Av1zi/Ebeep/include/Callbacks.h

#pragma once
#include <esp_sleep.h>
#include <time.h>

// ═══════════════════════════════════════════════════════════════
//  Callbacks.h
//  Buttons, display refresh, MQTT callbacks, and deep-sleep power
//  management — merged into one file so every function is defined
//  before it's used (checkButtons() and drawCurrentScreen() are
//  needed by the power-management refresh helpers below them).
//  Must be included AFTER all state files.
// ═══════════════════════════════════════════════════════════════

static float battVoltageEma = 0;  // mV, actual pack voltage (post-divider math)

void updateBattery() {
  // 8 samples is enough noise averaging on its own — the EMA below does
  // the real smoothing across calls, so we don't burn extra ADC time here.
  uint32_t sum = 0;
  for (int i = 0; i < 8; i++) sum += analogReadMilliVolts(A0);
  const float vBatSample = (sum / 8.0f) * BATTERY_DIVIDER_RATIO;

  battVoltageEma = (battVoltageEma == 0)
                     ? vBatSample
                     : battVoltageEma + BATTERY_EMA_ALPHA * (vBatSample - battVoltageEma);

  batteryPct = (int)((battVoltageEma - BATTERY_MIN_MV) * 100.0f / (BATTERY_MAX_MV - BATTERY_MIN_MV));
  batteryPct = constrain(batteryPct, 0, 100);
}

// Resets the active-mode timer. Call on any button press or incoming message.
void markActivity() {
  lastActivityMillis = millis();
}


bool pendingLeft  = false;
bool pendingMid   = false;
bool pendingRight = false;
bool isRefreshing = false;

// ── Button Handler ────────────────────────────────────────────
// Defined first so refreshDisplay() can call it.
void checkButtons() {
  bool curLeft  = digitalRead(BTN_LEFT);
  bool curMid   = digitalRead(BTN_SELECT);
  bool curRight = digitalRead(BTN_RIGHT);

  bool leftPressed  = (curLeft  == LOW && lastLeft  == HIGH);
  bool midPressed   = (curMid   == LOW && lastMid   == HIGH);
  bool rightPressed = (curRight == LOW && lastRight == HIGH);

  const unsigned long now = millis();

  if ((leftPressed || midPressed || rightPressed) && (now - lastBtnTime > DEBOUNCE_MS)) {
    lastBtnTime = now;
    markActivity();  // any press keeps the device in the active (modem-sleep) tier
    if (isRefreshing) {
      pendingLeft  |= leftPressed;
      pendingMid   |= midPressed;
      pendingRight |= rightPressed;
    } else {
      if (leftPressed || rightPressed) {
        heldButton    = leftPressed ? -1 : 1;
        holdStartTime = now;
        lastRepeatAt  = now;
      } else {
        heldButton = 0;
      }

      switch (currentState) {
        case STATE_HOME:      handleHomeInput      (leftPressed, midPressed, rightPressed); break;
        case STATE_INBOX:     handleInboxInput     (leftPressed, midPressed, rightPressed); break;
        case STATE_COMPOSE:   handleComposeInput   (leftPressed, midPressed, rightPressed); break;
        case STATE_SENT:      handleSentInput      (leftPressed, midPressed, rightPressed); break;
        case STATE_GAMES:     handleGamesInput     (leftPressed, midPressed, rightPressed); break;
        case STATE_TICTACTOE: handleTicTacToeInput (leftPressed, midPressed, rightPressed); break;
        case STATE_CONNECT4:  handleConnect4Input  (leftPressed, midPressed, rightPressed); break;
        case STATE_BLACKJACK: handleBlackjackInput(leftPressed, midPressed, rightPressed); break;
        default: break;
      }
    }
  }

  // Hold-scroll repeat (Compose, Games, and in-game selectors)
  if (heldButton != 0 &&
      (currentState == STATE_COMPOSE || currentState == STATE_GAMES ||
       currentState == STATE_TICTACTOE || currentState == STATE_CONNECT4 ||
       currentState == STATE_BLACKJACK)) {
    const bool stillHeld = (heldButton == -1) ? (curLeft == LOW) : (curRight == LOW);

    if (!stillHeld) {
      heldButton = 0;
    } else if ((now - holdStartTime >= HOLD_DELAY_MS) &&
               (now - lastRepeatAt  >= HOLD_REPEAT_MS)) {
      lastRepeatAt = now;
      const bool fL = (heldButton == -1);
      const bool fR = (heldButton ==  1);
      switch (currentState) {
        case STATE_COMPOSE:   handleComposeInput   (fL, false, fR); break;
        case STATE_GAMES:     handleGamesInput     (fL, false, fR); break;
        case STATE_TICTACTOE: handleTicTacToeInput (fL, false, fR); break;
        case STATE_CONNECT4:  handleConnect4Input  (fL, false, fR); break;
        case STATE_BLACKJACK: handleBlackjackInput (fL, false, fR); break;
        default: break;
      }
    }
  }

  lastLeft  = curLeft;
  lastMid   = curMid;
  lastRight = curRight;
}


// Draws whatever the current screen state is.
void drawCurrentScreen() {
  switch (currentState) {
    case STATE_HOME:      drawHome();      break;
    case STATE_INBOX:     drawInbox();     break;
    case STATE_COMPOSE:   drawCompose();   break;
    case STATE_SENT:      drawSent();      break;
    case STATE_GAMES:     drawGames();     break;
    case STATE_WIFI:      drawWifi();      break;
    case STATE_TICTACTOE: drawTicTacToe(); break;
    case STATE_CONNECT4:  drawConnect4();  break;
    case STATE_BLACKJACK: drawBlackjack(); break;
  }
}


// ── Display Refresh ───────────────────────────────────────────
// Calls checkButtons() mid-refresh so button presses aren't lost
// while the e-ink panel is transferring data.
void refreshDisplay() {
  isRefreshing = true;

  if (fastUpdate) {
    display.setPartialWindow(0, CONTENT_Y + 2, SCREEN_W, SCREEN_H - CONTENT_Y);
  } else {
    display.setFullWindow();
  }

  display.firstPage();
  do {
    display.fillScreen(GxEPD_WHITE);
    if (!fastUpdate) drawStatusBar(batteryPct);
    drawCurrentScreen();
    checkButtons();
  } while (display.nextPage());

  fastUpdate = false;
  isRefreshing = false;

  // Replay any button pressed during refresh
   if (pendingLeft || pendingMid || pendingRight) {
    bool l = pendingLeft, m = pendingMid, r = pendingRight;
    pendingLeft = pendingMid = pendingRight = false;
    switch (currentState) {
      case STATE_HOME:      handleHomeInput(l, m, r);       break;
      case STATE_INBOX:     handleInboxInput(l, m, r);      break;
      case STATE_COMPOSE:   handleComposeInput(l, m, r);    break;
      case STATE_SENT:      handleSentInput(l, m, r);       break;
      case STATE_GAMES:     handleGamesInput(l, m, r);      break;
      case STATE_TICTACTOE: handleTicTacToeInput(l, m, r);  break;
      case STATE_CONNECT4:  handleConnect4Input  (l, m, r); break;
      case STATE_BLACKJACK: handleBlackjackInput(l, m, r); break;
      default: break;
    }
  }
}


// ═══════════════════════════════════════════════════════════════
//  Power Management
//
//  Tiers, checked in priority order:
//    1. Active   — no deep sleep, WiFi modem-sleep only, for
//                  ACTIVE_TIMEOUT_MS after a button press or message.
//    2. Low batt — wake every WAKE_INTERVAL_LOWBATT_S  (batt < LOW_BATT_PCT)
//    3. Night    — wake every WAKE_INTERVAL_NIGHT_S    (00:00-08:00)
//    4. Default  — wake every WAKE_INTERVAL_DEFAULT_S
// ═══════════════════════════════════════════════════════════════

RTC_DATA_ATTR bool clockSynced = false;  // NTP only needs to succeed once — RTC keeps ticking through deep sleep
RTC_DATA_ATTR bool wifiWasOk   = true;   // persists across deep sleep — lets quickCheckAndMaybeSleep() tell if connectivity flipped since the last wake

bool isNightHours() {
  time_t now = time(nullptr);
  if (now < 100000) return false;
  struct tm t;
  localtime_r(&now, &t);
  return t.tm_hour >= NIGHT_START_HOUR && t.tm_hour < NIGHT_END_HOUR;
}

void syncNightClock() {
  if (clockSynced) return;
  configTzTime(TZ_STRING, "pool.ntp.org", "time.nist.gov");
  struct tm t;
  if (getLocalTime(&t, 2000)) clockSynced = true;
}

unsigned long currentWakeIntervalS() {
  if (batteryPct < LOW_BATT_PCT) return WAKE_INTERVAL_LOWBATT_S;
  if (isNightHours())            return WAKE_INTERVAL_NIGHT_S;
  return WAKE_INTERVAL_DEFAULT_S;
}

// Cheap periodic refresh (battery %, WiFi/MQTT icons only). Content is left
// alone — it only ever changes via an explicit needRefresh trigger, never
// silently, so redrawing it here on a timer would be wasted e-ink time and power.
void refreshStatusBarOnly() {
  display.setPartialWindow(0, 0, SCREEN_W, DIVIDER_TOP + 1);
  display.firstPage();
  do {
    display.fillScreen(GxEPD_WHITE);
    drawStatusBar(batteryPct);
    checkButtons();
  } while (display.nextPage());
}

// WiFi with a hard timeout instead of WiFiManager's blocking portal —
// credentials are already saved by now, this is just "is the radio good".
bool quickWifiConnect() {
  WiFi.mode(WIFI_STA);
  WiFi.begin();
  unsigned long start = millis();
  while (WiFi.status() != WL_CONNECTED && millis() - start < WIFI_CONNECT_TIMEOUT_MS) {
    delay(50);
  }
  return WiFi.status() == WL_CONNECTED;
}

// Never returns — drops the chip into deep sleep, waking on a timer
// or on a BTN_LEFT / BTN_SELECT press.
void enterDeepSleep(unsigned long seconds) {
  WiFi.disconnect(true);
  esp_sleep_pd_config(ESP_PD_DOMAIN_RTC_PERIPH, ESP_PD_OPTION_ON); // keeps the button pull-ups powered during sleep

  esp_sleep_enable_timer_wakeup((uint64_t)seconds * 1000000ULL);
  const uint64_t wakeMask = (1ULL << BTN_LEFT) | (1ULL << BTN_SELECT);
  esp_sleep_enable_ext1_wakeup(wakeMask, ESP_EXT1_WAKEUP_ANY_LOW);

  esp_deep_sleep_start();
}

bool quickCheckAndMaybeSleep() {
  updateBattery();

  bool gotMessage = false;
  bool wifiOk = quickWifiConnect();
  if (wifiOk) {
    wifiClient.setInsecure();
    wifiClient.setTimeout(WIFI_CONNECT_TIMEOUT_MS);
    mqttClient.setSocketTimeout(WIFI_CONNECT_TIMEOUT_MS / 1000);
    if (connectMQTT()) {
      unsigned long start = millis();
      while (millis() - start < MQTT_LISTEN_WINDOW_MS) {
        mqttClient.loop();
        if (hasUnreadMessage) { gotMessage = true; break; }
        delay(10);
      }
    }
  }
  
  if (gotMessage) return false;

  currentState = wifiOk ? STATE_HOME : STATE_WIFI;

  if (wifiOk != wifiWasOk) {
    // Connectivity flipped since the last wake — worth a real redraw so the
    // WiFi screen (or Home) actually shows, not just a stale battery %.
    fastUpdate = false;
    refreshDisplay();
  } else {
    refreshStatusBarOnly();
  }
  wifiWasOk = wifiOk;

  enterDeepSleep(currentWakeIntervalS());
  return true;  // unreachable
}

bool sleepWouldLoseState() {
  return inTicTacToe || TTT_pendingStart || inConnect4 || C4_pendingStart || messageLen > 0;
}

// Called every loop() tick. Drops to deep sleep once the active window
// (ACTIVE_TIMEOUT_MS since the last button press or message) has elapsed.
void handlePowerState() {
  if (millis() - lastActivityMillis < ACTIVE_TIMEOUT_MS) return;
  if (sleepWouldLoseState()) return;
  enterDeepSleep(currentWakeIntervalS());
}


// ── MQTT Callbacks ────────────────────────────────────────────
void gameReqHandler(char* payload) {
  if (strcmp(payload, "TTT_START") == 0) {
    if (TTT_pendingStart) {
      if (strcmp(BEEPER_ID, RECIVER_ID) < 0) TTT_becomeInitiator();
      else                                   TTT_joinAsOpponent();
    } else if (inTicTacToe) {
      inTicTacToe     = false;
      TTT_hasOpponent = true;
      TTT_flags       = TTT_NONE;
      if (currentState == STATE_TICTACTOE) {
        currentState = STATE_HOME;
        needRefresh  = true;
        fastUpdate   = false;
      }
    } else {
      TTT_hasOpponent = true;
    }
  } else if (strcmp(payload, "TTT_START_ACK") == 0) {
    if (TTT_pendingStart) TTT_becomeInitiator();
  } else if (strcmp(payload, "TTT_LEFT") == 0) {
    TTT_hasOpponent  = false;
    TTT_pendingStart = false;
    if (currentState == STATE_TICTACTOE) {
      inTicTacToe  = false;
      TTT_flags    = TTT_NONE;
      currentState = STATE_HOME;
      needRefresh  = true;
      fastUpdate   = false;
      return;
    }
  }

  // ── Connect 4 Logic ──
  else if (strcmp(payload, "C4_START") == 0) {
    if (C4_pendingStart) {
      if (strcmp(BEEPER_ID, RECIVER_ID) < 0) C4_becomeInitiator();
      else                                   C4_joinAsOpponent();
    } else if (inConnect4) {
      inConnect4     = false;
      C4_hasOpponent = true;
      C4_flags       = C4_NONE;
      if (currentState == STATE_CONNECT4) {
        currentState = STATE_HOME;
        needRefresh  = true;
        fastUpdate   = false;
      }
    } else {
      C4_hasOpponent = true;
    }
  } else if (strcmp(payload, "C4_START_ACK") == 0) {
    if (C4_pendingStart) C4_becomeInitiator();
  } else if (strcmp(payload, "C4_LEFT") == 0) {
    C4_hasOpponent  = false;
    C4_pendingStart = false;
    if (currentState == STATE_CONNECT4) {
      inConnect4   = false;
      C4_flags     = C4_NONE;
      currentState = STATE_HOME;
      needRefresh  = true;
      fastUpdate   = false;
      return;
    }
  }

  if (currentState == STATE_HOME || currentState == STATE_GAMES || 
      currentState == STATE_TICTACTOE || currentState == STATE_CONNECT4) {
    needRefresh = true;
    fastUpdate  = true;
  }
}

void onMessageReceived(char* topic, byte* payload, unsigned int length) {
  payload[length] = '\0';
  markActivity();

  const size_t idLen = strlen(BEEPER_ID);
  char* subTopic = topic + idLen;

  if (strcmp(subTopic, "/inbox") == 0) {
    Serial.println("Got msg in Inbox");
    uint8_t msgLen = (length < MAX_MSG_LEN) ? (uint8_t)length : MAX_MSG_LEN;
    memcpy(lastReceivedMessage, payload, msgLen);
    lastReceivedMessage[msgLen] = '\0';
    hasUnreadMessage = true;
    if (currentState == STATE_HOME) {
      needRefresh = true;
      fastUpdate  = true;
    } else if (currentState == STATE_INBOX) {
      needRefresh = true;
      fastUpdate  = false;
    }
  } else if (strcmp(subTopic, "/games") == 0) {
    Serial.println("Got msg in games");
    gameReqHandler((char*)payload);
  } else if (strncmp(subTopic, "/games/", 7) == 0) {
    if (strcmp(subTopic + 7, "TTT") == 0) {
      Serial.println("Got msg in TTT");
      checkTicTacToeMessages((char*)payload);
    } else if (strcmp(subTopic + 7, "C4") == 0) {
      Serial.println("Got msg in C4");
      checkConnect4Messages((char*)payload);
    }
  }
}
