Av1zi/Ebeep/include/display_utils.h

#pragma once

// ═══════════════════════════════════════════════════════════════
//  display_utils.h
//  Shared drawing primitives used by all state screens.
// ═══════════════════════════════════════════════════════════════


// Place text at pixel (x, y) — y is the font baseline.
void drawText(int16_t x, int16_t y, const char* text, const GFXfont* font) {
  display.setFont(font);
  display.setTextColor(GxEPD_BLACK);
  display.setCursor(x, y);
  display.print(text);
}

// Horizontally center text around cx at baseline y.
void drawCenteredText(int16_t cx, int16_t y, const char* text, const GFXfont* font) {
  display.setFont(font);
  display.setTextColor(GxEPD_BLACK);
  int16_t tbx, tby;
  uint16_t tbw, tbh;
  display.getTextBounds(text, 0, 0, &tbx, &tby, &tbw, &tbh);
  display.setCursor(cx - tbw / 2 - tbx, y);
  display.print(text);
}

// draw the top part
void drawStatusBar(int battPct) {
  battPct = constrain(battPct, 0, 100);

  // Title swaps to a warning below LOW_BATT_PCT — same slot, no layout changes needed.
  const char* title = (battPct <= LOW_BATT_PCT) ? "LOW BATT!" : "Ebeep";
  drawText(8, STATUS_TEXT_Y, title, &FreeMonoBold9pt7b);

  // Battery body + terminal nub
  constexpr int16_t bx = 248, by = 5, bw = 36, bh = 13;
  display.drawRect(bx, by, bw, bh, GxEPD_BLACK);
  display.fillRect(bx + bw, by + 4, 4, 5, GxEPD_BLACK);

  // Fill proportional to charge
  const int fillW = (battPct * (bw - 4)) / 100;
  if (fillW > 0) display.fillRect(bx + 2, by + 2, fillW, bh - 4, GxEPD_BLACK);

  // Percentage label, right-aligned against the battery icon
  char buf[6];
  snprintf(buf, sizeof(buf), "%d%%", battPct);
  display.setFont(&FreeMonoBold9pt7b);
  display.setTextColor(GxEPD_BLACK);
  int16_t tbx, tby;
  uint16_t tbw, tbh;
  display.getTextBounds(buf, 0, 0, &tbx, &tby, &tbw, &tbh);
  
  int16_t textStartX = bx - 5 - tbw - tbx;
  display.setCursor(textStartX, STATUS_TEXT_Y);
  display.print(buf);

  // ── Network Connection Status Icons ────────────────────────
  int16_t iconY = 7;
  int16_t mx = textStartX - 16; // MQTT Icon X coordinate
  int16_t wx = textStartX - 32; // WiFi Icon X coordinate

  // Draw WiFi Status Icon (3 rising signal bars)
  if (WiFi.status() == WL_CONNECTED) {
    display.fillRect(wx,     iconY + 6, 2, 4,  GxEPD_BLACK);
    display.fillRect(wx + 4, iconY + 3, 2, 7,  GxEPD_BLACK);
    display.fillRect(wx + 8, iconY,     2, 10, GxEPD_BLACK);
  } else {
    // Hollow outline bars + strike-through line if disconnected
    display.drawRect(wx,     iconY + 6, 2, 4,  GxEPD_BLACK);
    display.drawRect(wx + 4, iconY + 3, 2, 7,  GxEPD_BLACK);
    display.drawRect(wx + 8, iconY,     2, 10, GxEPD_BLACK);
    display.drawLine(wx - 2, iconY + 10, wx + 10, iconY, GxEPD_BLACK);
  }

  // Draw MQTT Status Icon (Custom 'M' Node)
  display.drawLine(mx,     iconY + 10, mx,     iconY,     GxEPD_BLACK);
  display.drawLine(mx,     iconY,     mx + 4, iconY + 5, GxEPD_BLACK);
  display.drawLine(mx + 4, iconY + 5, mx + 8, iconY,     GxEPD_BLACK);
  display.drawLine(mx + 8, iconY,     mx + 8, iconY + 10, GxEPD_BLACK);
  
  if (!mqttClient.connected()) {
    // Strike-through line if disconnected
    display.drawLine(mx - 2, iconY + 10, mx + 10, iconY, GxEPD_BLACK);
  }

  display.drawFastHLine(0, DIVIDER_TOP, SCREEN_W, GxEPD_BLACK);
}

void drawButtonHints(const char* left, const char* mid, const char* right) {
  display.drawFastHLine(0, DIVIDER_BOT, SCREEN_W, GxEPD_BLACK);
  display.drawFastVLine(COL_SPLIT1, DIVIDER_BOT, SCREEN_H - DIVIDER_BOT, GxEPD_BLACK);
  display.drawFastVLine(COL_SPLIT2, DIVIDER_BOT, SCREEN_H - DIVIDER_BOT, GxEPD_BLACK);
  drawCenteredText(COL1_CX, BTN_TEXT_Y, left,  &FreeMonoBold9pt7b);
  drawCenteredText(COL2_CX, BTN_TEXT_Y, mid,   &FreeMonoBold9pt7b);
  drawCenteredText(COL3_CX, BTN_TEXT_Y, right, &FreeMonoBold9pt7b);
}

// Shared "Yes/No" confirm popup, drawn centered over whatever's already on screen.
void drawConfirmPopup(const char* prompt) {
  constexpr int16_t pw = 210, ph = 48;
  constexpr int16_t px = (SCREEN_W - pw) / 2;
  const     int16_t py = CONTENT_Y + (CONTENT_H - ph) / 2;
  display.fillRect(px,     py,     pw,     ph,     GxEPD_WHITE);
  display.drawRect(px,     py,     pw,     ph,     GxEPD_BLACK);
  display.drawRect(px + 2, py + 2, pw - 4, ph - 4, GxEPD_BLACK);
  drawCenteredText(SCREEN_W / 2, py + 30, prompt, &FreeMonoBold9pt7b);
  drawButtonHints("No", "", "Yes");
}
